ExoFlex-Inc/Electrique/1-ExoFlexV2/1-STEP/LQH2HPN4R7MDRL.step

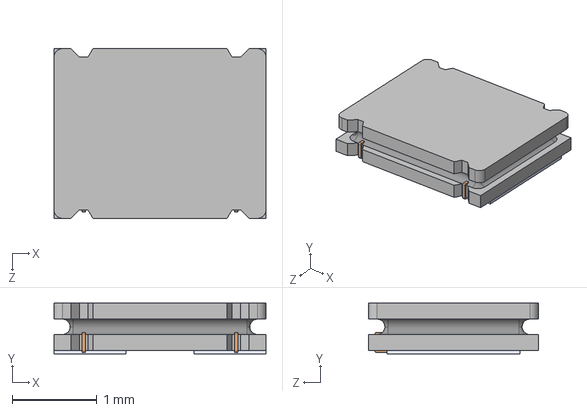
[picture p16: CAD file, 2024-07-17]
1-ExoFlexV2/1-STEP/LQH2HPN4R7MDRL.step
2.50 x 0.6 x 2.00 mm
