ExoFlex-Inc/Electrique/1-ExoFlexV2/1-STEP/SSW-108-01-G-D.step

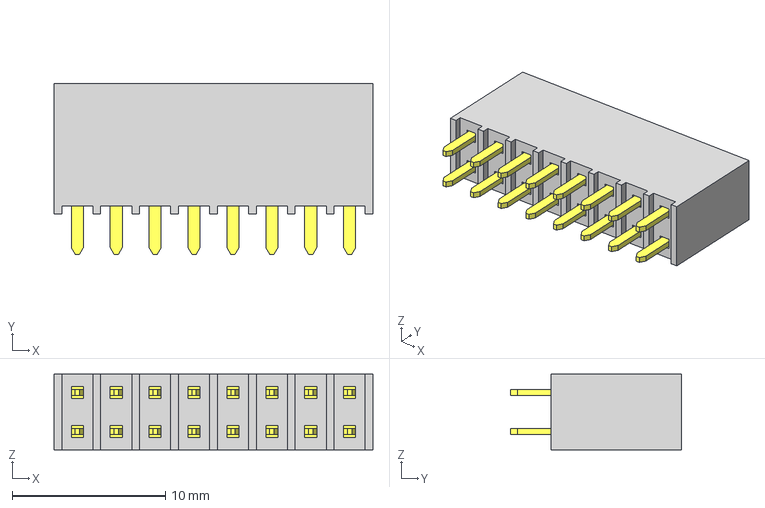
[picture p17: CAD file, 2024-07-17]
1-ExoFlexV2/1-STEP/SSW-108-01-G-D.step
20.8 x 11.2 x 4.95 mm
T1SSW-108-01-G-D
P2SSW-108-01-G-D
