ExoFlex-Inc/Electrique/1-ExoFlexV2/1-STEP/SSW-115-01-G-D.step

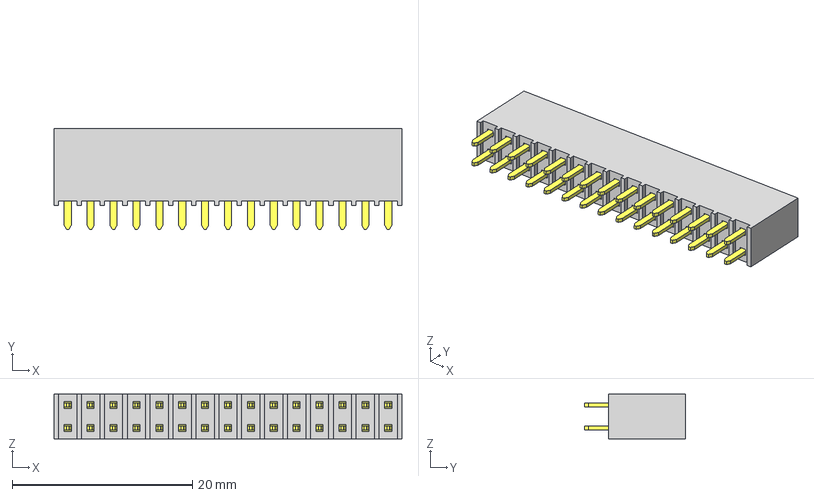
[picture p19: CAD file, 2024-07-17]
1-ExoFlexV2/1-STEP/SSW-115-01-G-D.step
38.6 x 11.2 x 4.95 mm
T1SSW-115-01-G-D
P2SSW-115-01-G-D
