ExoFlex-Inc/Electrique/1-ExoFlexV2/1-STEP/LBR2012T100K.step

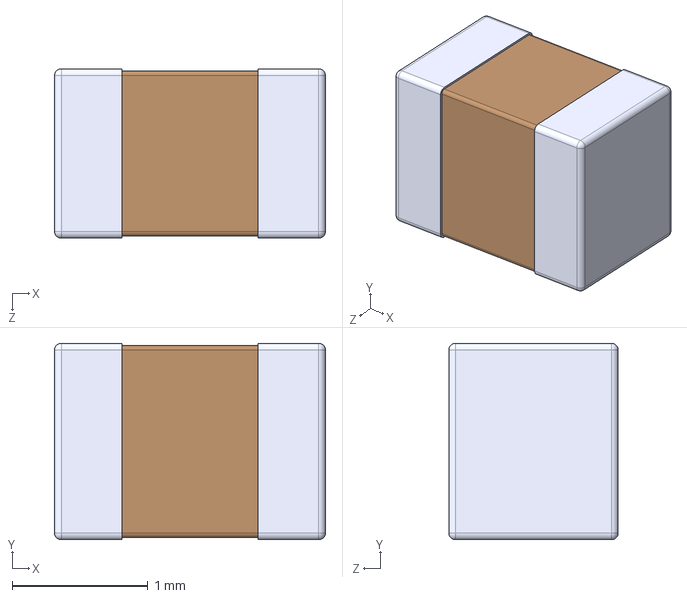
[picture p20: CAD file, 2024-07-11]
1-ExoFlexV2/1-STEP/LBR2012T100K.step
2.00 x 1.45 x 1.25 mm
