ExoFlex-Inc/Electrique/1-ExoFlexV2/1-STEP/KCM55TR7YA336MH01L.step

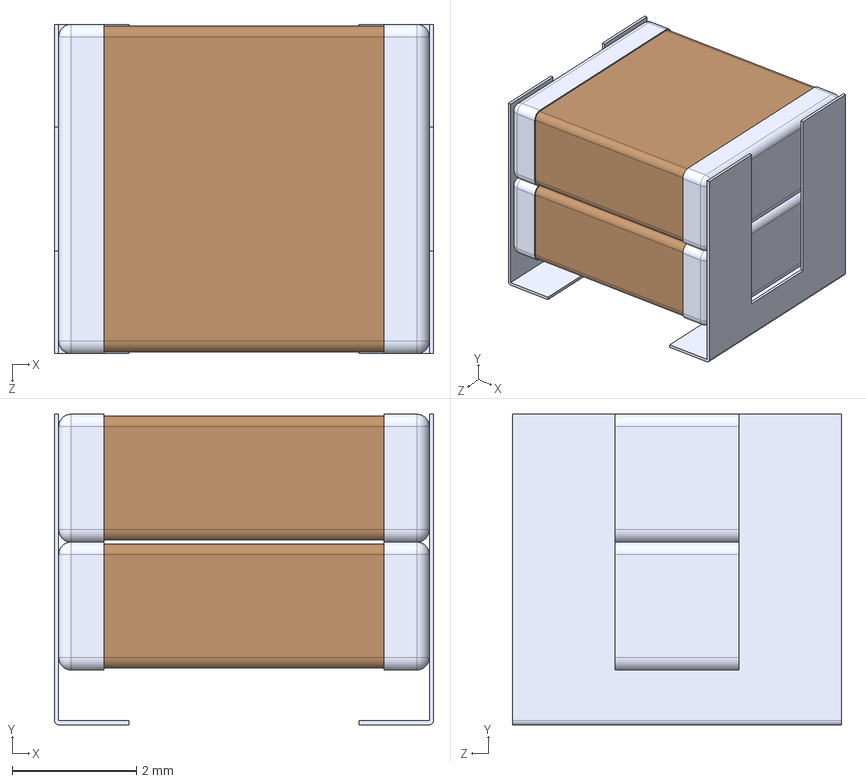
[picture p21: CAD file, 2024-07-10]
1-ExoFlexV2/1-STEP/KCM55TR7YA336MH01L.step
6.10 x 5.00 x 5.30 mm
