ExoFlex-Inc/Electrique/1-ExoFlexV2/1-STEP/CAP_PC_10X12P7_NCH.step

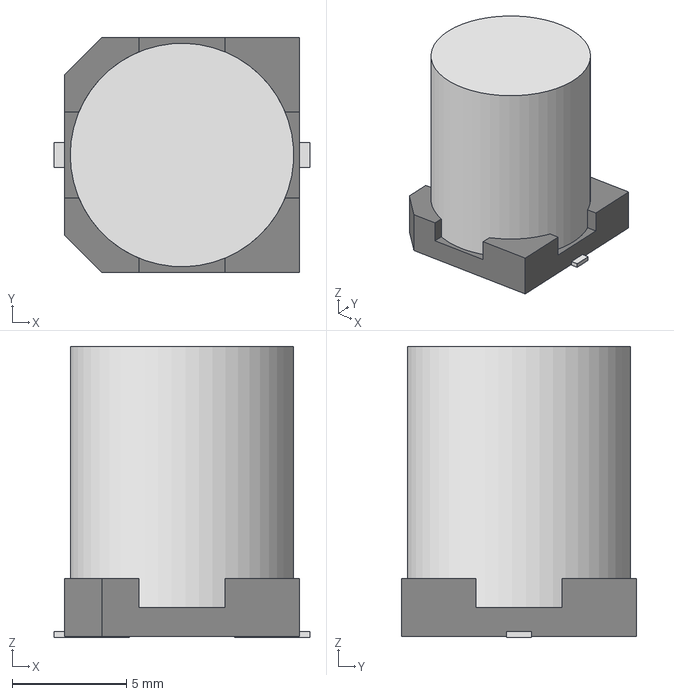
[picture p22: CAD file, 2024-07-10]
1-ExoFlexV2/1-STEP/CAP_PC_10X12P7_NCH.step
11.2 x 10.3 x 12.8 mm
