ExoFlex-Inc/Electrique/1-ExoFlexV2/1-STEP/DGK0008A.stp

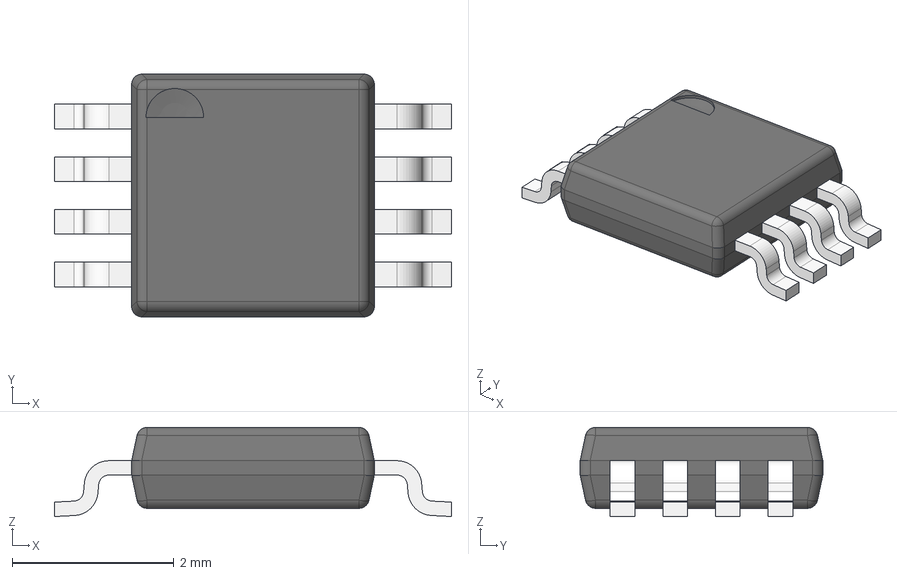
[picture p23: CAD file, 2024-07-10]
1-ExoFlexV2/1-STEP/DGK0008A.stp
4.90 x 3.00 x 1.10 mm
BODY_MUA08A
LEAD_MUA08A x 8
