ExoFlex-Inc/Electrique/1-ExoFlexV2/1-STEP/T491B105K035AT.step

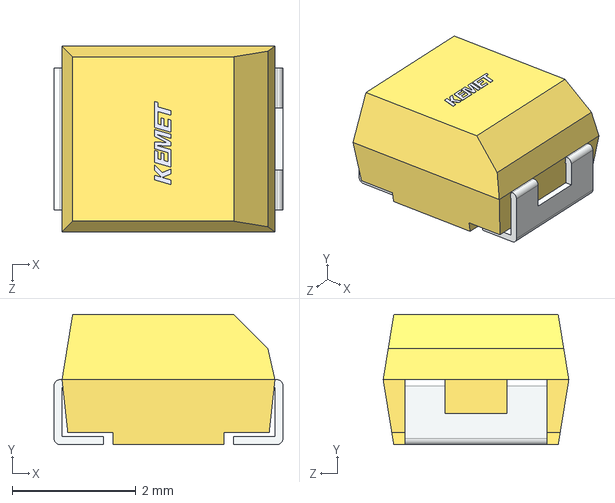
[picture p24: CAD file, 2024-07-10]
1-ExoFlexV2/1-STEP/T491B105K035AT.step
3.70 x 2.11 x 3.00 mm
