ExoFlex-Inc/Electrique/1-ExoFlexV2/1-STEP/DCY0004A.stp

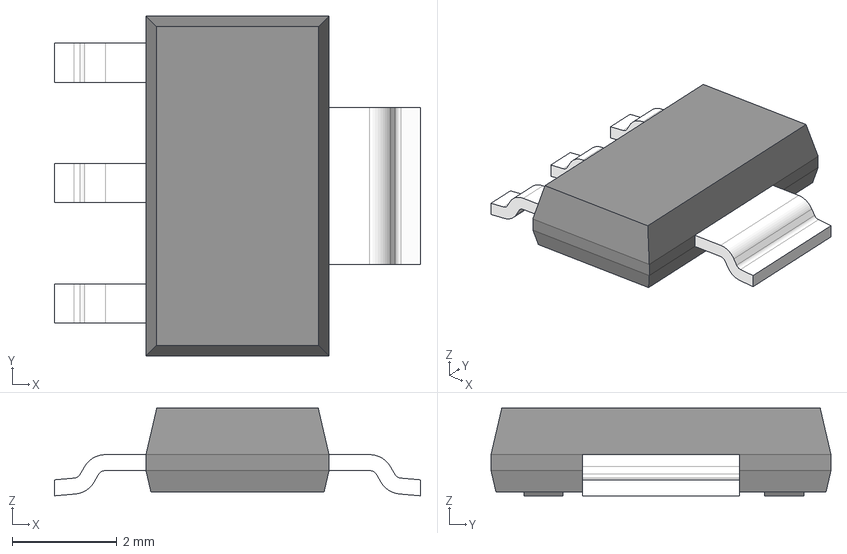
[picture p25: CAD file, 2024-07-10]
1-ExoFlexV2/1-STEP/DCY0004A.stp
7.00 x 6.50 x 1.68 mm
BODY-SOT
LEAD-SOT x 3
LEAD-SOT-WIDE
PIN1-ID
