ExoFlex-Inc/Electrique/1-ExoFlexV2/1-STEP/NDY0011A.stp

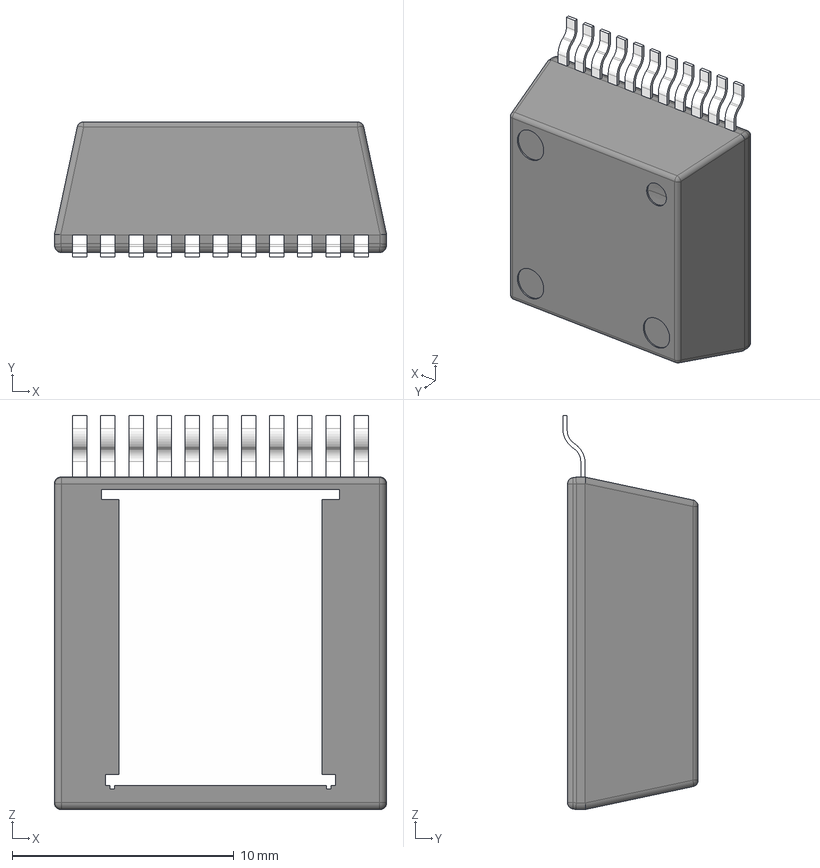
[picture p26: CAD file, 2024-07-10]
1-ExoFlexV2/1-STEP/NDY0011A.stp
15.0 x 6.11 x 17.8 mm
LF_TOP_TZA11A
LF_BTM_TZA11A
BODY_TZA11A
LEAD_TZA11A x 11
