ExoFlex-Inc/Electrique/1-ExoFlexV2/1-STEP/EEE_FKiV101P.stp

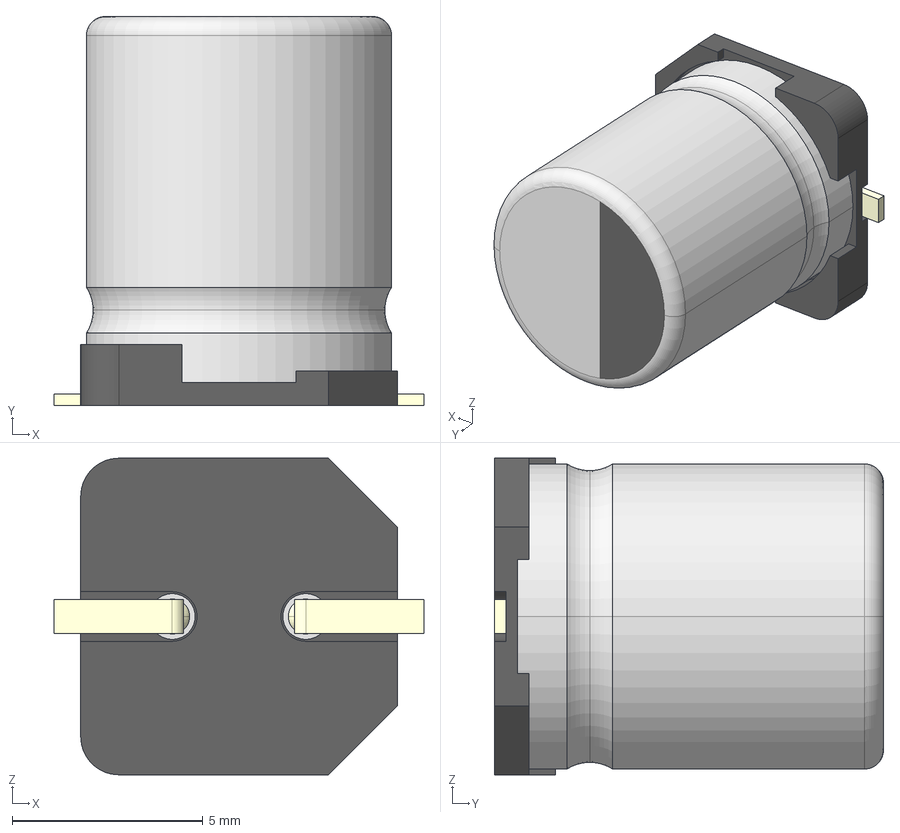
[picture p27: CAD file, 2024-07-10]
1-ExoFlexV2/1-STEP/EEE_FKiV101P.stp
9.70 x 10.2 x 8.30 mm
