ExoFlex-Inc/Electrique/1-ExoFlexV2/1-STEP/CAPC220145_88N_KEM.step

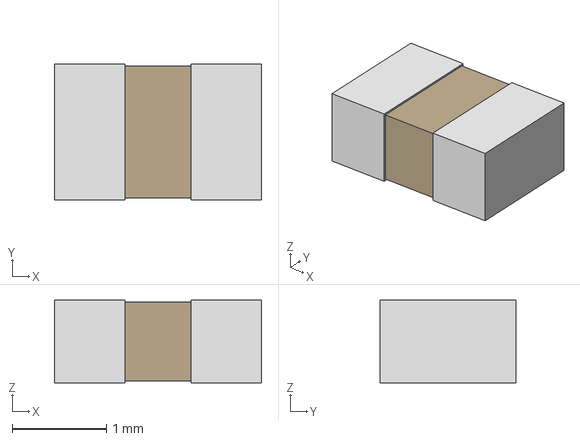
[picture p28: CAD file, 2024-07-10]
1-ExoFlexV2/1-STEP/CAPC220145_88N_KEM.step
2.20 x 1.45 x 0.88 mm
