ExoFlex-Inc/Electrique/1-ExoFlexV2/1-STEP/SN74F251BDR.step

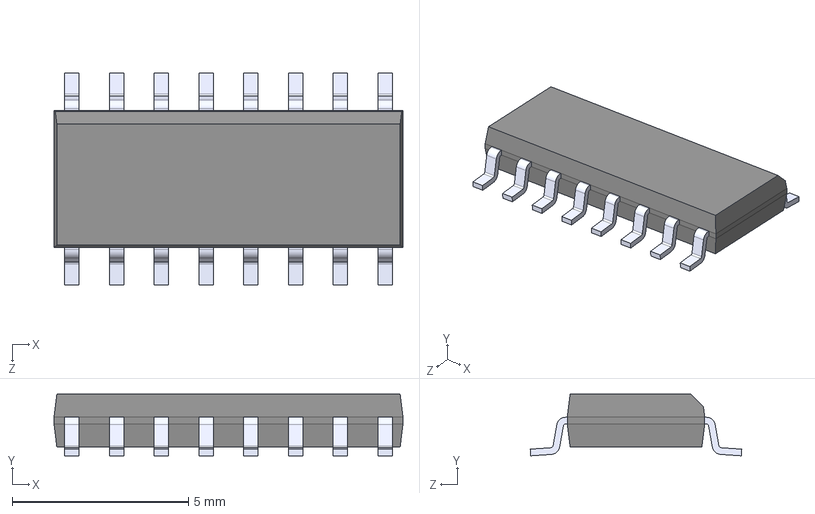
[picture p29: CAD file, 2024-06-28]
1-ExoFlexV2/1-STEP/SN74F251BDR.step
9.90 x 1.75 x 6.00 mm
