ExoFlex-Inc/Electrique/1-ExoFlexV2/1-STEP/SOT403-1_NXP.step

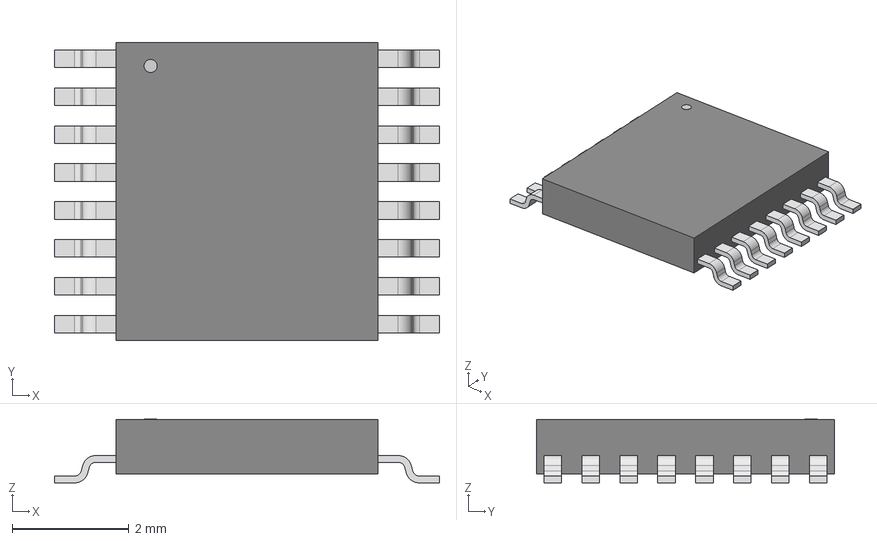
[picture p30: CAD file, 2024-06-28]
1-ExoFlexV2/1-STEP/SOT403-1_NXP.step
6.60 x 5.11 x 1.09 mm
