ExoFlex-Inc/Electrique/1-ExoFlexV2/1-STEP/PW0016A.stp

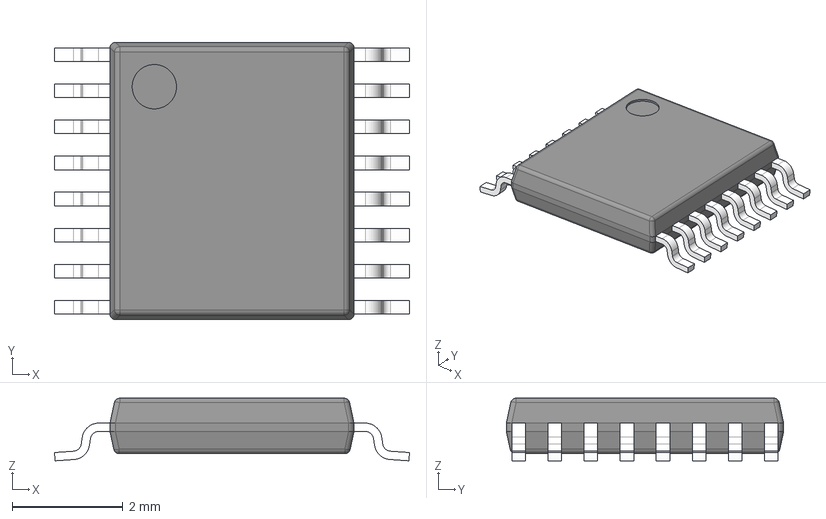
[picture p31: CAD file, 2024-06-27]
1-ExoFlexV2/1-STEP/PW0016A.stp
6.40 x 5.00 x 1.13 mm
BODY-TSSOP
LEAD-TSSOP x 16
PIN1
