ExoFlex-Inc/Electrique/1-ExoFlexV2/1-STEP/SN74LVC3G14DCUT.step

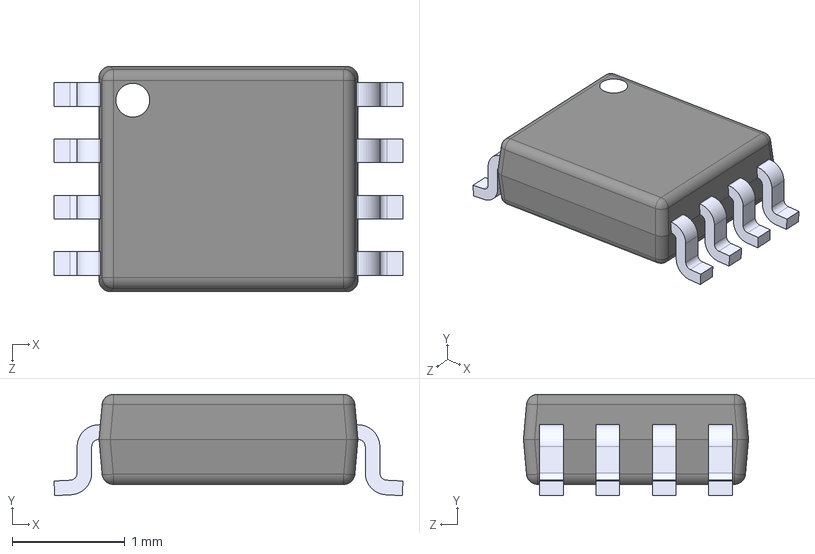
[picture p32: CAD file, 2024-06-27]
1-ExoFlexV2/1-STEP/SN74LVC3G14DCUT.step
3.10 x 0.9 x 2.00 mm
