ExoFlex-Inc/Electrique/1-ExoFlexV2/1-STEP/D0008A.stp

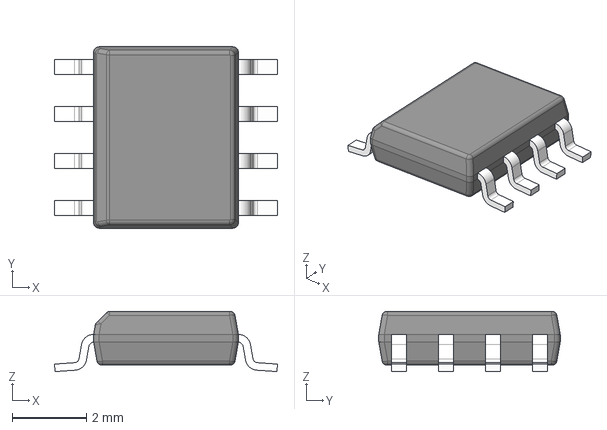
[picture p33: CAD file, 2024-06-27]
1-ExoFlexV2/1-STEP/D0008A.stp
6.02 x 4.90 x 1.63 mm
BODY-SO
LEAD-D0008A x 8
