ExoFlex-Inc/Electrique/1-ExoFlexV2/1-STEP/801-87-002-10-001101.STEP

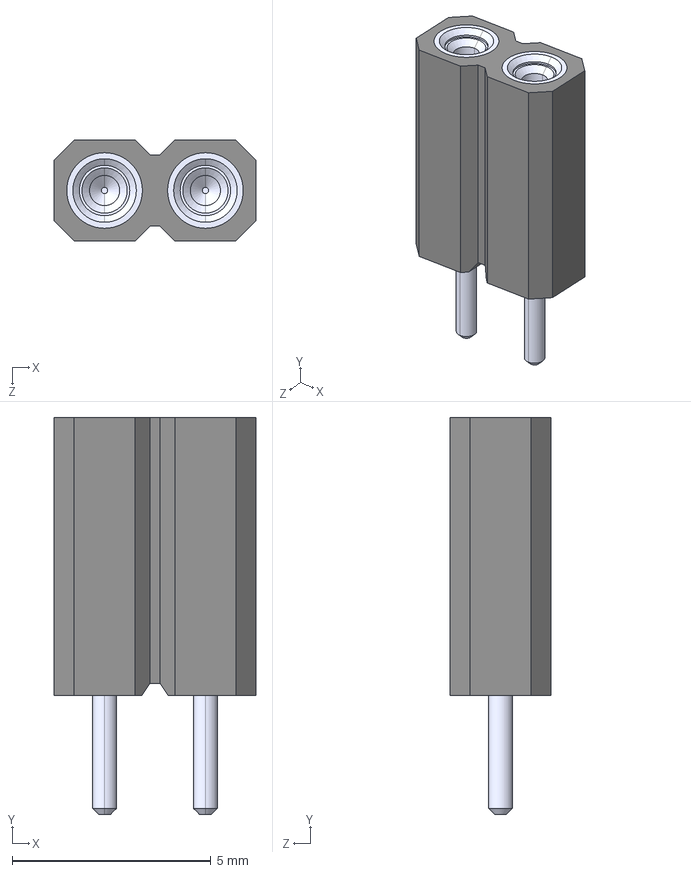
[picture p34: CAD file, 2024-06-27]
1-ExoFlexV2/1-STEP/801-87-002-10-001101.STEP
5.08 x 10.0 x 2.54 mm
