ExoFlex-Inc/Electrique/1-ExoFlexV2/1-STEP/SN74LVC1G08DBVR.step

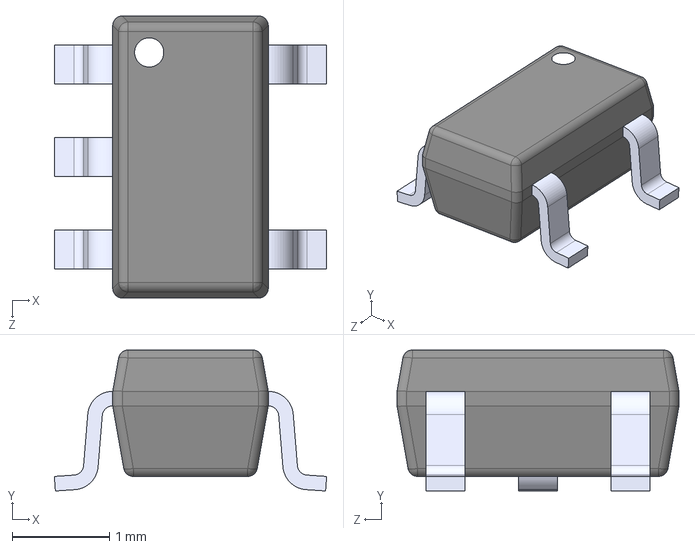
[picture p35: CAD file, 2024-06-27]
1-ExoFlexV2/1-STEP/SN74LVC1G08DBVR.step
2.80 x 1.45 x 2.90 mm
