ExoFlex-Inc/Electrique/1-ExoFlexV2/1-STEP/3362P-1-102LF.step

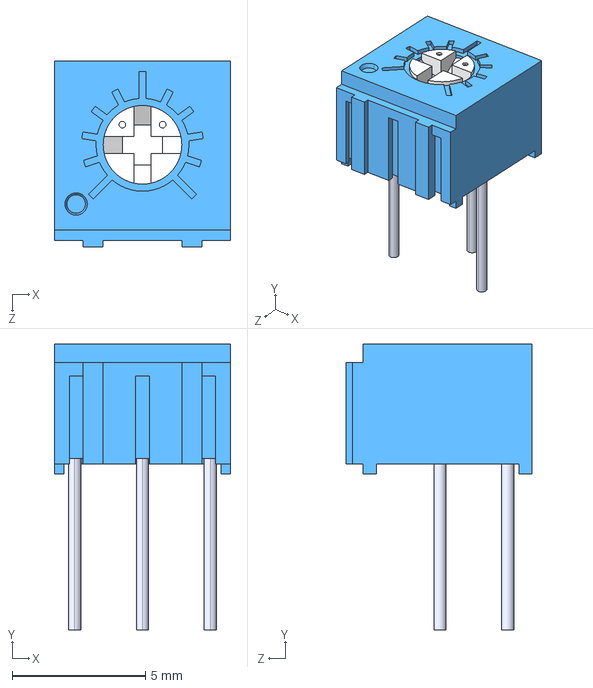
[picture p36: CAD file, 2024-06-27]
1-ExoFlexV2/1-STEP/3362P-1-102LF.step
6.60 x 10.7 x 6.99 mm
