ExoFlex-Inc/Electrique/1-ExoFlexV2/1-STEP/DRL0005A.stp

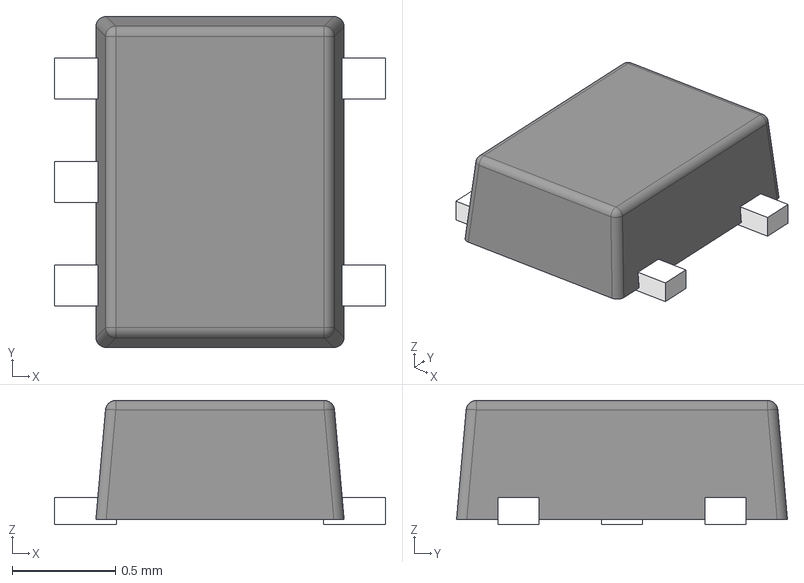
[picture p37: CAD file, 2024-06-27]
1-ExoFlexV2/1-STEP/DRL0005A.stp
1.60 x 1.60 x 0.6 mm
FRAME-DRL0005A
BODY-SOT
PIN1-ID
