ExoFlex-Inc/Electrique/1-ExoFlexV2/1-STEP/86A.STEP

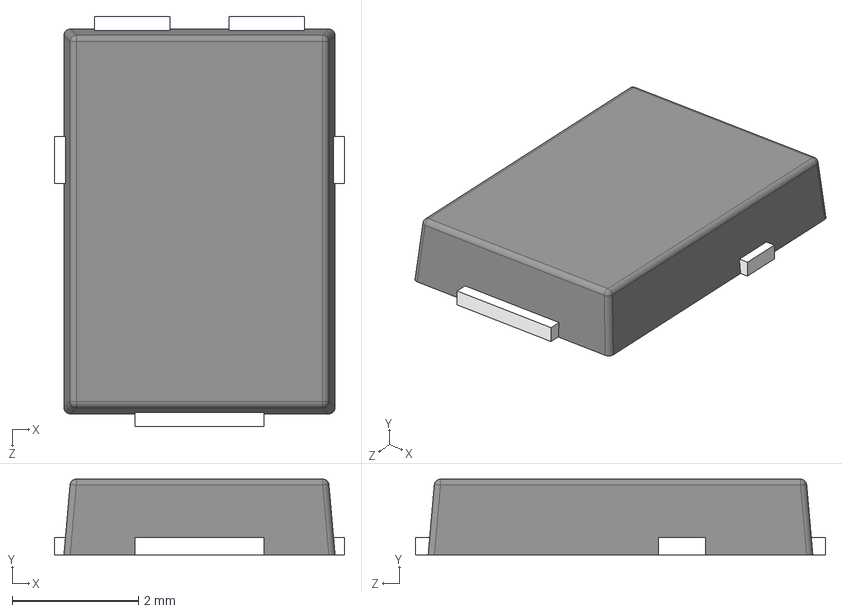
[picture p38: CAD file, 2024-06-27]
1-ExoFlexV2/1-STEP/86A.STEP
4.60 x 1.20 x 6.50 mm
