ExoFlex-Inc/Electrique/1-ExoFlexV2/1-STEP/STPS20M100SG-TR.step

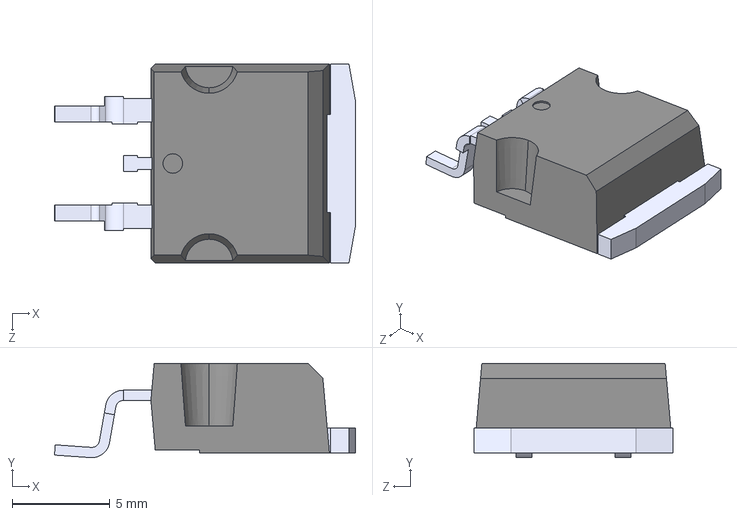
[picture p39: CAD file, 2024-06-27]
1-ExoFlexV2/1-STEP/STPS20M100SG-TR.step
15.4 x 4.83 x 10.2 mm
