ExoFlex-Inc/Electrique/1-ExoFlexV2/1-STEP/5005.step

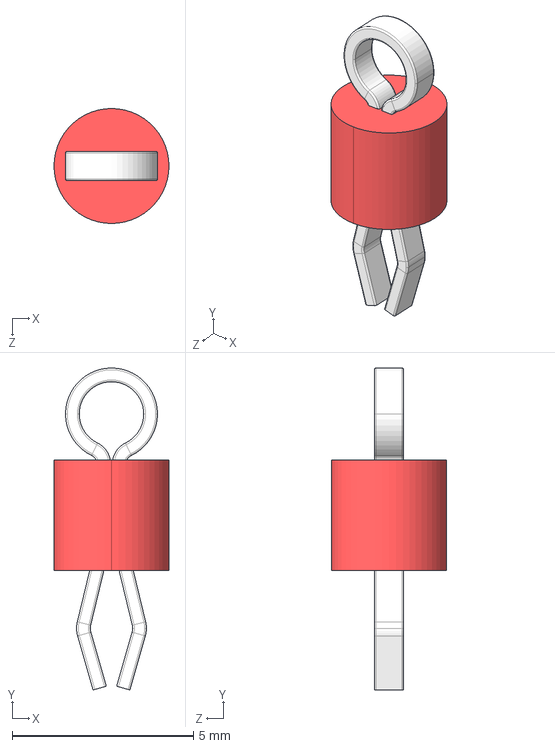
[picture p40: CAD file, 2024-03-21]
1-ExoFlexV2/1-STEP/5005.step
3.17 x 8.89 x 3.17 mm
