ExoFlex-Inc/Electrique/1-ExoFlexV2/1-STEP/TPS7A4701RGWR.step

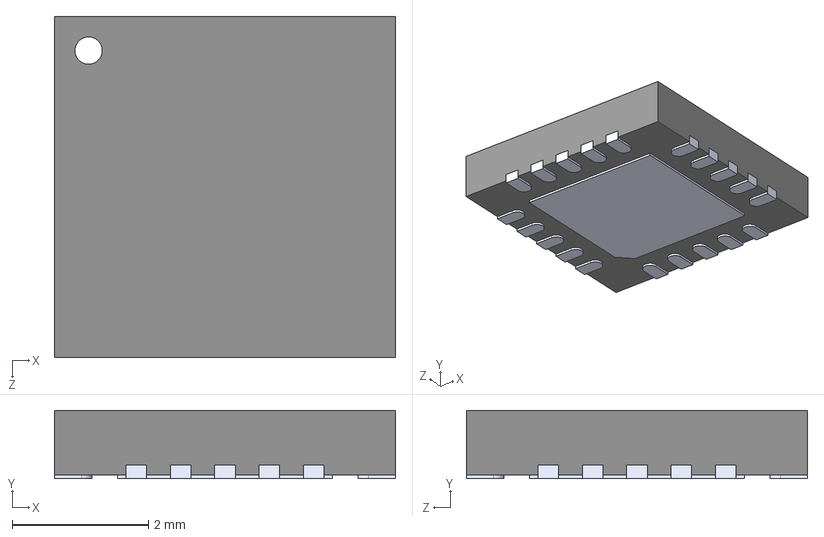
[picture p41: CAD file, 2024-03-21]
1-ExoFlexV2/1-STEP/TPS7A4701RGWR.step
5.00 x 1.00 x 5.00 mm
