ExoFlex-Inc/Electrique/1-ExoFlexV2/1-STEP/MAX6818EAP_T.step

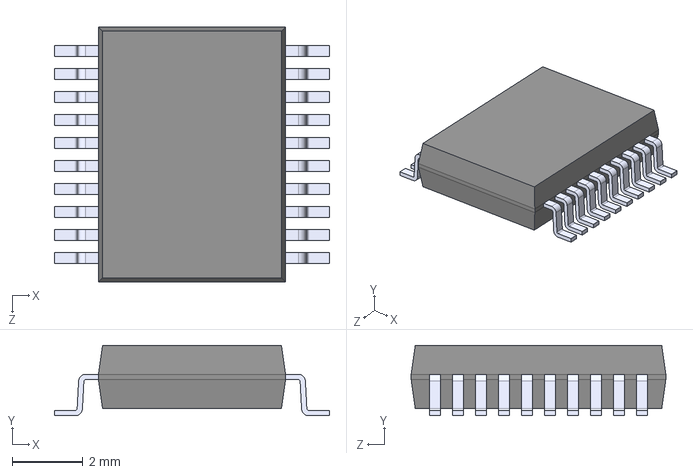
[picture p42: CAD file, 2024-03-21]
1-ExoFlexV2/1-STEP/MAX6818EAP_T.step
7.78 x 1.99 x 7.20 mm
